RobertGawron/GammaSpectrometer/03_SubsystemDesign/DigitalLogic/Source/Interfaces/README.md

# Interfaces

Modules that implement communication protocols, bus connections, or signal adaptation for external devices and internal design interconnects.
