RobertGawron/GammaSpectrometer/03_SubsystemDesign/DetectorAssembly/01_Models_Source/01_OpenSCAD/01_ScintillationCrystalHolder/README.md

# Purpose

3D-printed holder for the scintillator crystal and the reflective material surrounding it.

Note: Main.scad is the main file which should be used for the final render and .step export.
