RobertGawron/GammaSpectrometer/05_Verification/DigitalLogic/UnitVerification/Core/README.md

# Core Testbench

Testbenches for [Core modules](../../Source/Core/).
