RobertGawron/GammaSpectrometer/05_Verification/DigitalLogic/UnitVerification/Integration/README.md

# Integration Testbench

This directory contains integration-level testbenches.

## Purpose
Testbenches in this directory verify interaction between multiple modules and confirm correct behavior of integrated design functions.
