RobertGawron/GammaSpectrometer/05_Verification/DigitalLogic/UnitVerification/Peripherals/README.md

# Peripheral Testbench

Testbenches for [Peripheral modules](../../Source/Peripherals/).
