RobertGawron/GammaSpectrometer/03_SubsystemDesign/ElectronicHardware/Model/AFE.asc

C1: cap; 2.2n
C2: cap; 150p
C3: cap; 1p
C4: cap; 1p
C5: cap; 100p
C6: cap; 100p
C7: cap; 100p
R1: res; 2k
R2: res; 50
R3: res; 620R
R4: res; 620R
R5: res; 50
R6: res; 499
R7: res; 499
R8: res; 50
R9: res; 50
R10: res; 10
U2: AD8139
U3: LTC6268
Named nets: VCC_5V, VREF, OUT_P, OUT_N, SIPM, 0, CSA_OUT
