RobertGawron/GammaSpectrometer/05_Verification/ElectronicHardware/Simulation/Analog/ANA-001_OutputNoise/02_SimulationModel/TbNoise.asc

C1: cap; 7p
C3: cap; 7p
I1: current; 0; AC 1
U1: AFE
V1: voltage; 2.5
V2: voltage; 2.5
V4: voltage; 5
V5: voltage; 5
V6: voltage; 2
Named nets: 0, Vcc_2v5, Vee_2v5, Vcc_5v, Vee_5v, Vref, OUT_P, OUT_N
From ADC datasheet:
Input Capacitance: 7 pF
Input capacitance refers to the effective capacitance 
between one differential input pin and AVSS.
 
There is no info about input resistance. We will not model it.
.meas NOISE OutputNoise_RMS INTEG V(onoise)
.noise V(OUT_P,OUT_N) I1 dec 200 0.01 20Meg
.include "../../../../../../03_SubsystemDesign/ElectronicHardware/Model/AFE.sub"
