RobertGawron/GammaSpectrometer/05_Verification/ElectronicHardware/Simulation/Analog/ANA-002_PulseLinearity/02_SimulationModel/TbTransientPulseSlow.asc

B1: bi; I = -{Iamp}*exp(-(time-t0)/tau_scint)*if(time>t0,1,0)
C1: cap; 7p
C2: cap; 3n4
C3: cap; 7p
C4: cap; 3n4
U1: AFE
V1: voltage; 2.5
V2: voltage; 2.5
V4: voltage; 5
V5: voltage; 5
V6: voltage; 2.5
Named nets: 0, Vcc_2v5, Vee_2v5, Vcc_5v, Vee_5v, Vref, OUT_P, OUT_N
From ADC datasheet:
Input Capacitance: 7 pF
Input capacitance refers to the effective capacitance 
between one differential input pin and AVSS.
 
There is no info about input resistance. We will not model it.
.include "../../../../../../03_SubsystemDesign/ElectronicHardware/Model/AFE.sub"
Pulse model assumptions for AFE validation
 
Sensor: MICROFC-60035-SMT (2 devices in parallel)
Microcell recharge time constant tau_cell = 95 ns (datasheet)
NaI(Tl) scintillation decay time approx 230 ns (dominant pulse tail)
 
Effective current pulse decay constant tau_eff approx 200-250 ns
 
Pulse width PW >= 5*tau_eff to ensure full charge delivery
Example: tau_eff = 230 ns -> 5*tau = 1.15 us
 
Period T >= PW + 3*tau_eff to prevent pulse overlap
Recommended T >= 3 us for clean pulse separation
 
Note:
CSA feedback time constant tau_feedback = Rf * Cf = 100M * 270p = 27 ms
Baseline recovery is therefore much slower than pulse width.
Simulation period is chosen for pulse separation, not full baseline reset.
 
Rise/Fall time TR/TF = 1 ns
(negligible compared to system bandwidth 3-6 MHz)
 
Iamp is swept to produce Vout up to >= 2.0 Vpp
 
Used to verify:
  - Sensor maximum amplitude
  - Front-end gain scaling
  - ADC full-scale utilization
  - Saturation margin
 
Goals:
  - Avoid clipping at maximum expected energy
  - Avoid under-utilizing ADC dynamic range
.param tau_scint=230n
.param t0=100n
 
.step param Iamp list 0.2m 0.5m 1m 2m 4m 6m 8m 10m 15m
 
 
 
.tran 0 6u 0 1n
