RobertGawron/GammaSpectrometer/05_Verification/ElectronicHardware/Simulation/Analog/ANA-004_TransientRiseTime/02_SimulationModel/TbBandwidthStep.asc

C1: cap; 7p
C3: cap; 7p
I1: current; PULSE(0 1u 1u 5n 5n 100u 200u); AC 1
U1: AFE
V1: voltage; 2.5
V2: voltage; 2.5
V4: voltage; 5
V5: voltage; 5
V6: voltage; 2
Named nets: 0, Vcc_2v5, Vee_2v5, Vcc_5v, Vee_5v, Vref, OUT_P, OUT_N
From ADC datasheet:
Input Capacitance: 7 pF
Input capacitance refers to the effective capacitance 
between one differential input pin and AVSS.
 
There is no info about input resistance. We will not model it.
.tran 0 50u 0 1n
.include "../../../../../../03_SubsystemDesign/ElectronicHardware/Model/AFE.sub"
